sastles-com/isolation-sphere-solo-xiao/kiban/EasyEDA/outputs/pcb/boardA_placement_top.png

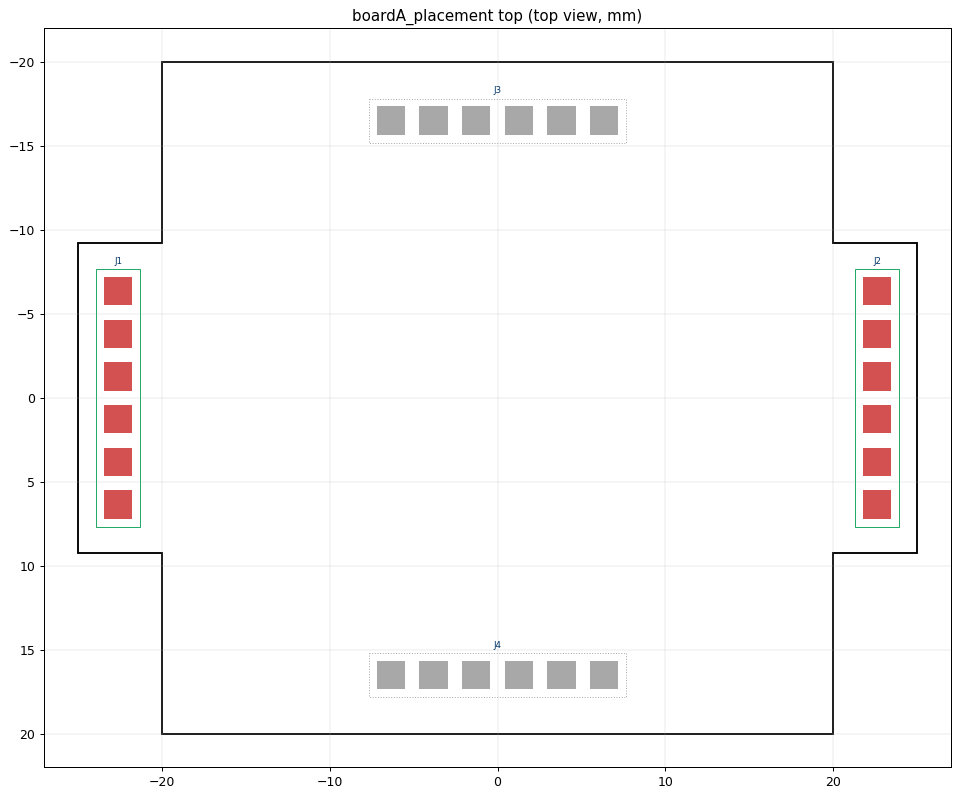
kiban/EasyEDA/outputs/pcb/boardA_placement_top.png
