sastles-com/isolation-sphere-solo-xiao/kiban/EasyEDA/outputs/pcb/boardB_placement_bottom.png

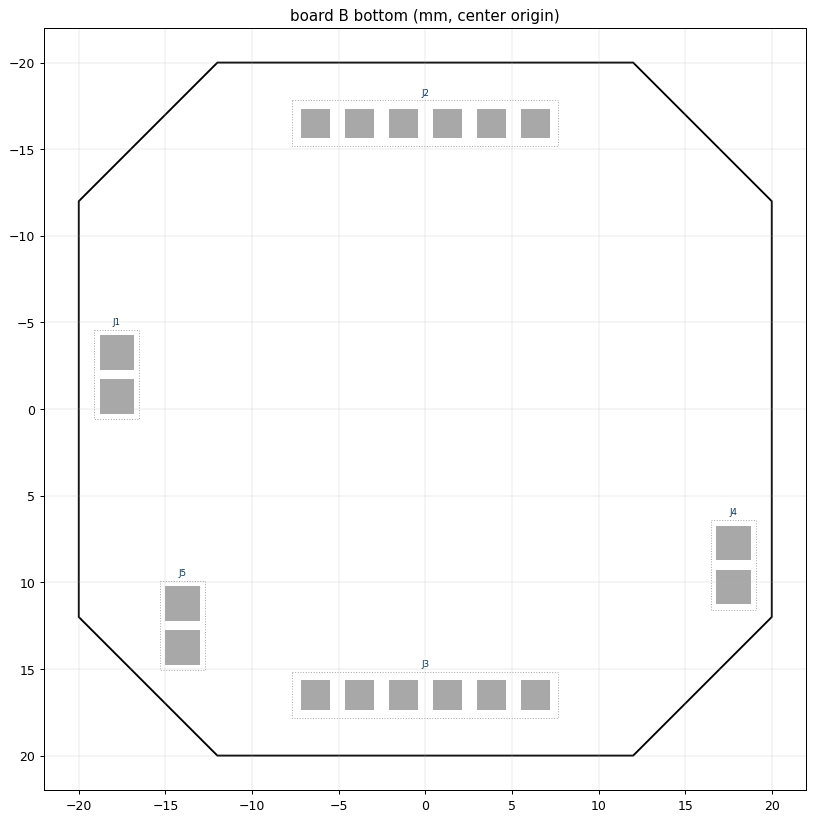
kiban/EasyEDA/outputs/pcb/boardB_placement_bottom.png
