sastles-com/isolation-sphere-solo-xiao/kiban/EasyEDA/outputs/pcb/boardB_placement_top.png

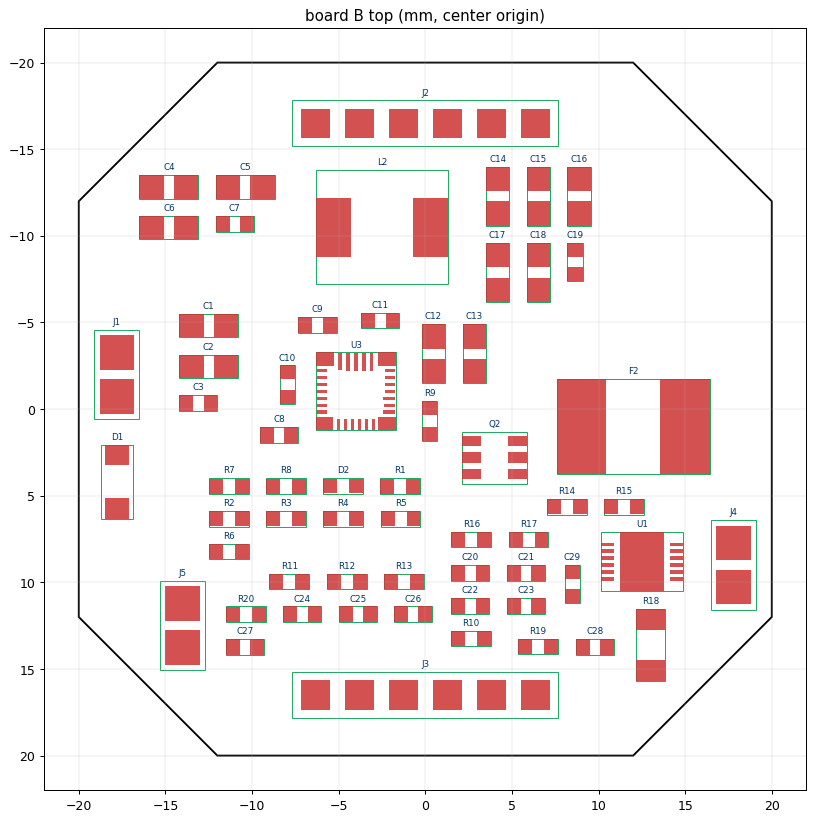
kiban/EasyEDA/outputs/pcb/boardB_placement_top.png
