sastles-com/isolation-sphere-solo-xiao/kiban/EasyEDA/outputs/pcb/boardB_routed.png

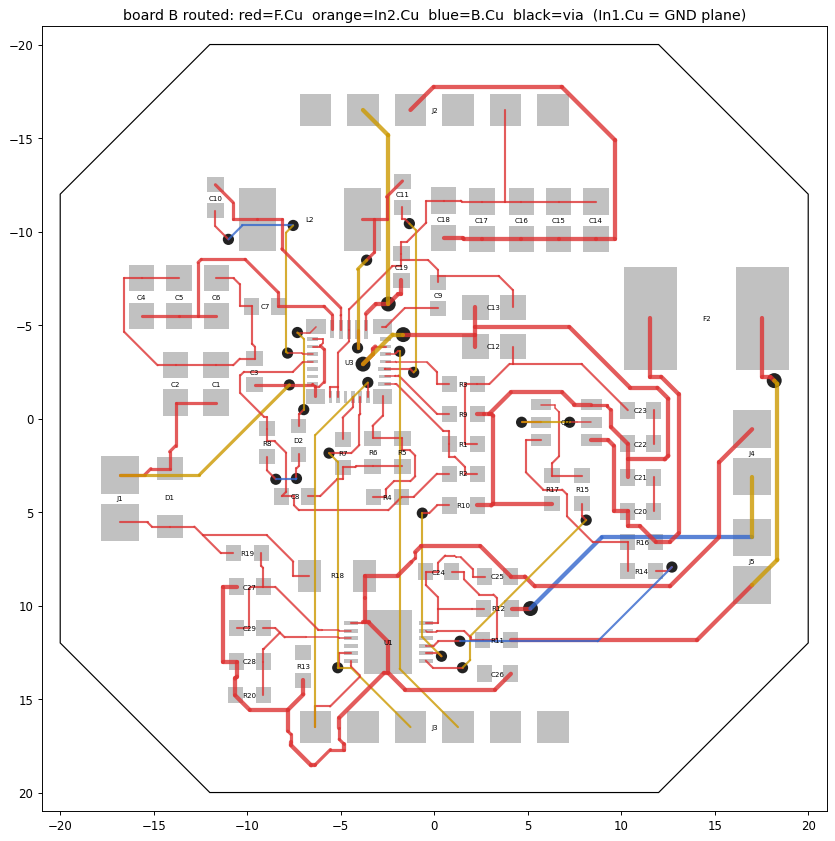
kiban/EasyEDA/outputs/pcb/boardB_routed.png
